azerimaker/promini-node/hardware/ProMini-Node-v1.0-50x50.kicad_sch

## KiCad design hardware/ProMini-Node-v1.0-50x50.kicad_sch (2024-09-15, an earlier design)

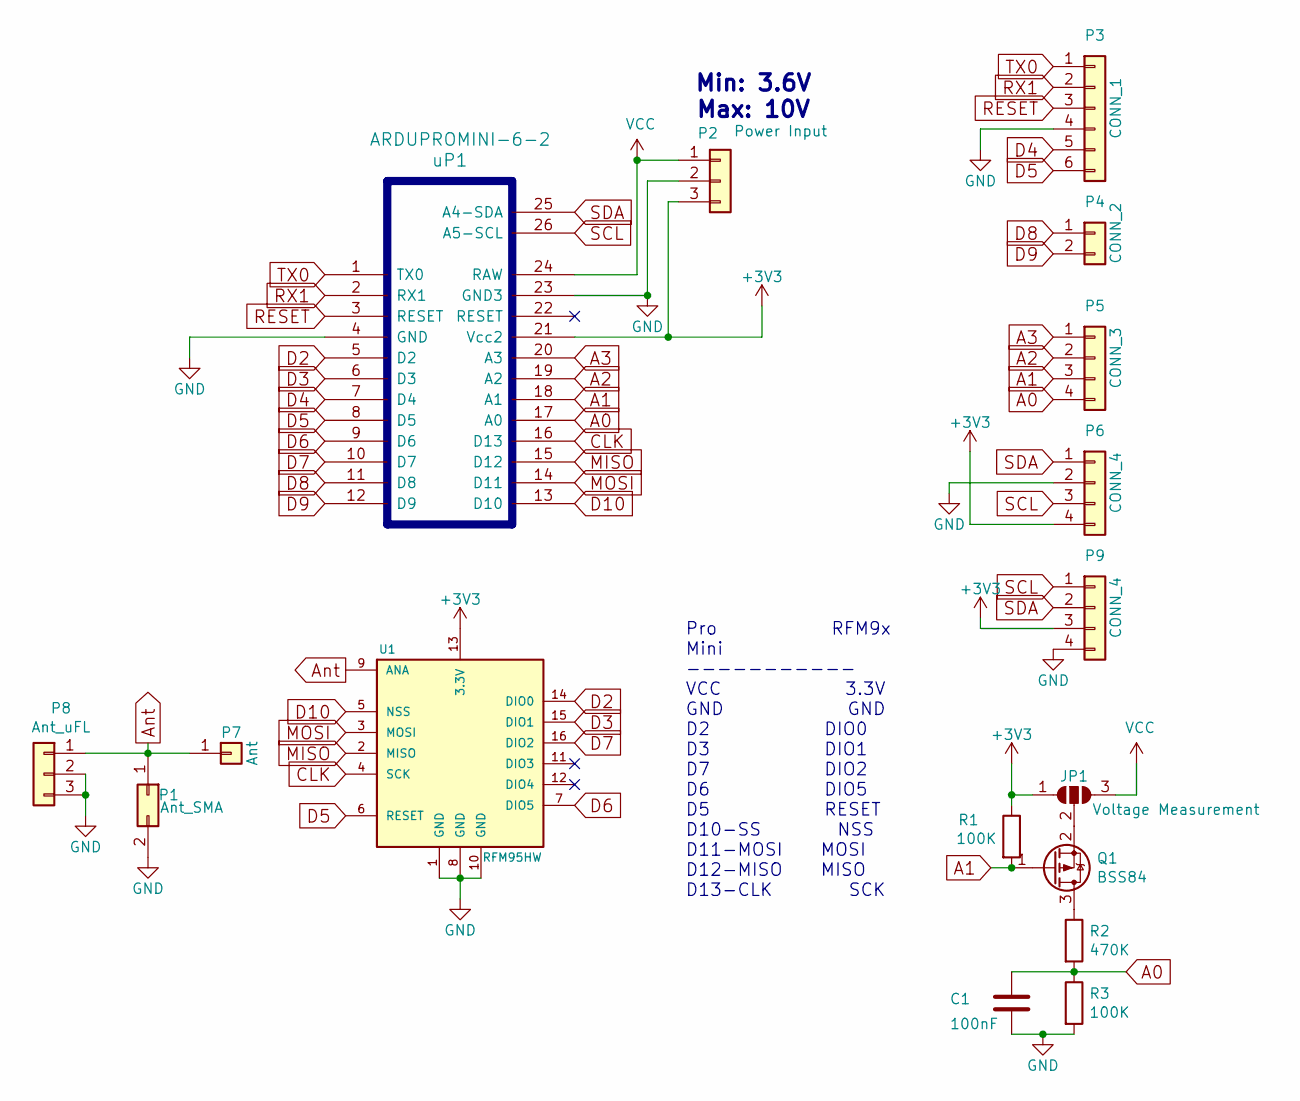
[picture p8: schematic ProMini-Node-v1.0-50x50.kicad_sch]

Parts:
C1: 100nF; C_0805_2012Metric_Pad1.15x1.40mm_HandSolder
JP1: Voltage Measurement; SolderJumper-3_P1.3mm_Open_RoundedPad1.0x1.5mm_NumberLabels
P1: Ant_SMA; SMA_EDGE
P2: Power Input; PINHEAD1-3
P3: CONN_1; Pin_Header_Straight_1x06
P4: CONN_2; Pin_Header_Straight_1x02
P5: CONN_3; Pin_Header_Straight_1x04
P6: CONN_4; Pin_Header_Straight_1x04
P7: Ant; PINTST
P8: Ant_uFL; U.FL-COAX
P9: CONN_4; NS-Tech_Grove_1x04_P2mm_Vertical
Q1: BSS84; SOT-23
R1, R3: 100K; R_0805_2012Metric_Pad1.15x1.40mm_HandSolder
R2: 470K; R_0805_2012Metric_Pad1.15x1.40mm_HandSolder
U1: RFM95HW; RFM69HW_SMD_Handsoldering-Narrow
uP1: ARDUPROMINI-6-2; pro_mini-26

Connections:
+3V3: JP1.1 (A), P2.3, P6.4, P9.3, R1.1, U1.13 (3.3V), uP1.21 (Vcc2)
A0: C1.1, P5.4, R2.2, R3.1, uP1.17 (A0)
A1: P5.3, Q1.1 (G), R1.2, uP1.18 (A1)
A2: P5.2, uP1.19 (A2)
A3: P5.1, uP1.20 (A3)
Ant: P1.1, P7.1, P8.1, U1.9 (ANA)
CLK: U1.4 (SCK), uP1.16 (D13)
D2: U1.14 (DIO0), uP1.5 (D2)
D3: U1.15 (DIO1), uP1.6 (D3)
D4: P3.5, uP1.7 (D4)
D5: P3.6, U1.6 (RESET), uP1.8 (D5)
D6: U1.7 (DIO5), uP1.9 (D6)
D7: U1.16 (DIO2), uP1.10 (D7)
D8: P4.1, uP1.11 (D8)
D9: P4.2, uP1.12 (D9)
D10: U1.5 (NSS), uP1.13 (D10)
GND: C1.2, P1.2, P2.2, P3.4, P6.2, P8.2, P8.3, P9.4, R3.2, U1.1 (GND), U1.8 (GND), U1.10 (GND), uP1.4 (GND), uP1.23 (GND3)
MISO: U1.2 (MISO), uP1.15 (D12)
MOSI: U1.3 (MOSI), uP1.14 (D11)
unnamed: JP1.2 (C), Q1.2 (S)
unnamed: Q1.3 (D), R2.1
RESET: P3.3, uP1.3 (RESET)
RX1: P3.2, uP1.2 (RX1)
SCL: P6.3, P9.1, uP1.26 (A5-SCL)
SDA: P6.1, P9.2, uP1.25 (A4-SDA)
TX0: P3.1, uP1.1 (TX0)
VCC: JP1.3 (B), P2.1, uP1.24 (RAW)

Notes on the sheet:
Pro RFM9x Mini ----------- VCC 3.3V GND GND D2 DIO0 D3 DIO1 D7 DIO2 D6 DIO5 D5 RESET D10-SS NSS D11-MOSI MOSI D12-MISO MISO D13-CLK SCK
Min: 3.6V Max: 10V
